Digruttola2468/MatrizLedArduino/RTC3231/RTC3231.ino

#include<Wire.h>
#include<RTClib.h>

/* Conection RTC3231
SDA --> 20 SDA 
SCL --> 21 SCL 
*/

RTC_DS3231 rtc;

void setup() {
  Serial.begin(9600);

  if( !rtc.begin() ){
    Serial.println("Modulo RTC no encontrado");
    while(1);
  }
  rtc.adjust(DateTime(__DATE__,__TIME__));
}

void loop() {
  DateTime fecha = rtc.now();

  Serial.print(fecha.day());
  Serial.print("/");
   
  Serial.print(fecha.month());
  Serial.print("/");
   
  Serial.print(fecha.year());
  Serial.print("   ");


  
  Serial.print(fecha.hour());
  Serial.print(":");
   
  Serial.print(fecha.minute());
  Serial.print(":");

  Serial.print(fecha.second());
  Serial.println();

  delay(1000);
}
